taroz/TouchRTKStation/doc/TRS4-1.jpg

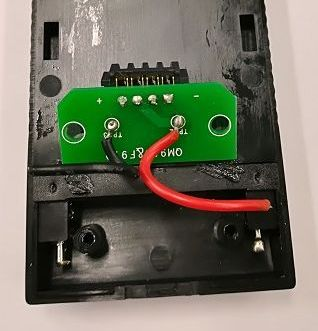
doc/TRS4-1.jpg
